gtortone/KeyPortari/firmware/src/PS2Keymaps.cpp

/*
  PS2Keymaps.cpp - PS2Keymaps library
  Copyright (c) 2025 Free Software Foundation.  All right reserved.
  Written by Wolfgang Stubig <w.stubig@firmaplus.de> 2025

  extracted from PS2Keyboard library written by Christian Weichel <info@32leaves.net>
  for more information you can read the original wiki in arduino.cc
  at http://www.arduino.cc/playground/Main/PS2Keyboard
  or http://www.pjrc.com/teensy/td_libs_PS2Keyboard.html
*/

// http://www.quadibloc.com/comp/scan.htm
// http://www.computer-engineering.org/ps2keyboard/scancodes2.html

// These arrays provide a simple key map, to turn scan codes into ISO8859
// output.  For US, DE and FR keyboards.
//

#include "PS2Keymaps.h"

const PROGMEM PS2Keymap_t PS2Keymap_US = {
  // without shift
	{0, PS2_F9, 0, PS2_F5, PS2_F3, PS2_F1, PS2_F2, PS2_F12,
	0, PS2_F10, PS2_F8, PS2_F6, PS2_F4, PS2_TAB, '`', 0,
	0, 0 /*Lalt*/, 0 /*Lshift*/, 0, 0 /*Lctrl*/, 'q', '1', 0,
	0, 0, 'z', 's', 'a', 'w', '2', 0,
	0, 'c', 'x', 'd', 'e', '4', '3', 0,
	0, ' ', 'v', 'f', 't', 'r', '5', 0,
	0, 'n', 'b', 'h', 'g', 'y', '6', 0,
	0, 0, 'm', 'j', 'u', '7', '8', 0,
	0, ',', 'k', 'i', 'o', '0', '9', 0,
	0, '.', '/', 'l', ';', 'p', '-', 0,
	0, 0, '\'', 0, '[', '=', 0, 0,
	0 /*CapsLock*/, 0 /*Rshift*/, PS2_ENTER /*Enter*/, ']', 0, '\\', 0, 0,
	0, 0, 0, 0, 0, 0, PS2_BACKSPACE, 0,
	0, '1', 0, '4', '7', 0, 0, 0,
	'0', '.', '2', '5', '6', '8', PS2_ESC, 0 /*NumLock*/,
	PS2_F11, '+', '3', '-', '*', '9', PS2_SCROLL, 0,
	0, 0, 0, PS2_F7 },
  // with shift
	{0, PS2_F9, 0, PS2_F5, PS2_F3, PS2_F1, PS2_F2, PS2_F12,
	0, PS2_F10, PS2_F8, PS2_F6, PS2_F4, PS2_TAB, '~', 0,
	0, 0 /*Lalt*/, 0 /*Lshift*/, 0, 0 /*Lctrl*/, 'Q', '!', 0,
	0, 0, 'Z', 'S', 'A', 'W', '@', 0,
	0, 'C', 'X', 'D', 'E', '$', '#', 0,
	0, ' ', 'V', 'F', 'T', 'R', '%', 0,
	0, 'N', 'B', 'H', 'G', 'Y', '^', 0,
	0, 0, 'M', 'J', 'U', '&', '*', 0,
	0, '<', 'K', 'I', 'O', ')', '(', 0,
	0, '>', '?', 'L', ':', 'P', '_', 0,
	0, 0, '"', 0, '{', '+', 0, 0,
	0 /*CapsLock*/, 0 /*Rshift*/, PS2_ENTER /*Enter*/, '}', 0, '|', 0, 0,
	0, 0, 0, 0, 0, 0, PS2_BACKSPACE, 0,
	0, '1', 0, '4', '7', 0, 0, 0,
	'0', '.', '2', '5', '6', '8', PS2_ESC, 0 /*NumLock*/,
	PS2_F11, '+', '3', '-', '*', '9', PS2_SCROLL, 0,
	0, 0, 0, PS2_F7 },
	0
};


const PROGMEM PS2Keymap_t PS2Keymap_German = {
  // without shift
	{0, PS2_F9, 0, PS2_F5, PS2_F3, PS2_F1, PS2_F2, PS2_F12,
	0, PS2_F10, PS2_F8, PS2_F6, PS2_F4, PS2_TAB, '^', 0,
	0, 0 /*Lalt*/, 0 /*Lshift*/, 0, 0 /*Lctrl*/, 'q', '1', 0,
	0, 0, 'y', 's', 'a', 'w', '2', 0,
	0, 'c', 'x', 'd', 'e', '4', '3', 0,
	0, ' ', 'v', 'f', 't', 'r', '5', 0,
	0, 'n', 'b', 'h', 'g', 'z', '6', 0,
	0, 0, 'm', 'j', 'u', '7', '8', 0,
	0, ',', 'k', 'i', 'o', '0', '9', 0,
	0, '.', '-', 'l', PS2_o_DIAERESIS, 'p', PS2_SHARP_S, 0,
	0, 0, PS2_a_DIAERESIS, 0, PS2_u_DIAERESIS, '\'', 0, 0,
	0 /*CapsLock*/, 0 /*Rshift*/, PS2_ENTER /*Enter*/, '+', 0, '#', 0, 0,
	0, '<', 0, 0, 0, 0, PS2_BACKSPACE, 0,
	0, '1', 0, '4', '7', 0, 0, 0,
	'0', '.', '2', '5', '6', '8', PS2_ESC, 0 /*NumLock*/,
	PS2_F11, '+', '3', '-', '*', '9', PS2_SCROLL, 0,
	0, 0, 0, PS2_F7 },
  // with shift
	{0, PS2_F9, 0, PS2_F5, PS2_F3, PS2_F1, PS2_F2, PS2_F12,
	0, PS2_F10, PS2_F8, PS2_F6, PS2_F4, PS2_TAB, PS2_DEGREE_SIGN, 0,
	0, 0 /*Lalt*/, 0 /*Lshift*/, 0, 0 /*Lctrl*/, 'Q', '!', 0,
	0, 0, 'Y', 'S', 'A', 'W', '"', 0,
	0, 'C', 'X', 'D', 'E', '$', PS2_SECTION_SIGN, 0,
	0, ' ', 'V', 'F', 'T', 'R', '%', 0,
	0, 'N', 'B', 'H', 'G', 'Z', '&', 0,
	0, 0, 'M', 'J', 'U', '/', '(', 0,
	0, ';', 'K', 'I', 'O', '=', ')', 0,
	0, ':', '_', 'L', PS2_O_DIAERESIS, 'P', '?', 0,
	0, 0, PS2_A_DIAERESIS, 0, PS2_U_DIAERESIS, '`', 0, 0,
	0 /*CapsLock*/, 0 /*Rshift*/, PS2_ENTER /*Enter*/, '*', 0, '\'', 0, 0,
	0, '>', 0, 0, 0, 0, PS2_BACKSPACE, 0,
	0, '1', 0, '4', '7', 0, 0, 0,
	'0', '.', '2', '5', '6', '8', PS2_ESC, 0 /*NumLock*/,
	PS2_F11, '+', '3', '-', '*', '9', PS2_SCROLL, 0,
	0, 0, 0, PS2_F7 },
	1,
  // with altgr
	{0, PS2_F9, 0, PS2_F5, PS2_F3, PS2_F1, PS2_F2, PS2_F12,
	0, PS2_F10, PS2_F8, PS2_F6, PS2_F4, PS2_TAB, 0, 0,
	0, 0 /*Lalt*/, 0 /*Lshift*/, 0, 0 /*Lctrl*/, '@', 0, 0,
	0, 0, 0, 0, 0, 0, PS2_SUPERSCRIPT_TWO, 0,
	0, 0, 0, 0, PS2_CURRENCY_SIGN, 0, PS2_SUPERSCRIPT_THREE, 0,
	0, 0, 0, 0, 0, 0, 0, 0,
	0, 0, 0, 0, 0, 0, 0, 0,
	0, 0, PS2_MICRO_SIGN, 0, 0, '{', '[', 0,
	0, 0, 0, 0, 0, '}', ']', 0,
	0, 0, 0, 0, 0, 0, '\\', 0,
	0, 0, 0, 0, 0, 0, 0, 0,
	0 /*CapsLock*/, 0 /*Rshift*/, PS2_ENTER /*Enter*/, '~', 0, '#', 0, 0,
	0, '|', 0, 0, 0, 0, PS2_BACKSPACE, 0,
	0, '1', 0, '4', '7', 0, 0, 0,
	'0', '.', '2', '5', '6', '8', PS2_ESC, 0 /*NumLock*/,
	PS2_F11, '+', '3', '-', '*', '9', PS2_SCROLL, 0,
	0, 0, 0, PS2_F7 }
};


const PROGMEM PS2Keymap_t PS2Keymap_French = {
  // without shift
	{0, PS2_F9, 0, PS2_F5, PS2_F3, PS2_F1, PS2_F2, PS2_F12,
	0, PS2_F10, PS2_F8, PS2_F6, PS2_F4, PS2_TAB, PS2_SUPERSCRIPT_TWO, 0,
	0, 0 /*Lalt*/, 0 /*Lshift*/, 0, 0 /*Lctrl*/, 'a', '&', 0,
	0, 0, 'w', 's', 'q', 'z', PS2_e_ACUTE, 0,
	0, 'c', 'x', 'd', 'e', '\'', '"', 0,
	0, ' ', 'v', 'f', 't', 'r', '(', 0,
	0, 'n', 'b', 'h', 'g', 'y', '-', 0,
	0, 0, ',', 'j', 'u', PS2_e_GRAVE, '_', 0,
	0, ';', 'k', 'i', 'o', PS2_a_GRAVE, PS2_c_CEDILLA, 0,
	0, ':', '!', 'l', 'm', 'p', ')', 0,
	0, 0, PS2_u_GRAVE, 0, '^', '=', 0, 0,
	0 /*CapsLock*/, 0 /*Rshift*/, PS2_ENTER /*Enter*/, '$', 0, '*', 0, 0,
	0, '<', 0, 0, 0, 0, PS2_BACKSPACE, 0,
	0, '1', 0, '4', '7', 0, 0, 0,
	'0', '.', '2', '5', '6', '8', PS2_ESC, 0 /*NumLock*/,
	PS2_F11, '+', '3', '-', '*', '9', PS2_SCROLL, 0,
	0, 0, 0, PS2_F7 },
  // with shift
	{0, PS2_F9, 0, PS2_F5, PS2_F3, PS2_F1, PS2_F2, PS2_F12,
	0, PS2_F10, PS2_F8, PS2_F6, PS2_F4, PS2_TAB, 0, 0,
	0, 0 /*Lalt*/, 0 /*Lshift*/, 0, 0 /*Lctrl*/, 'A', '1', 0,
	0, 0, 'W', 'S', 'Q', 'Z', '2', 0,
	0, 'C', 'X', 'D', 'E', '4', '3', 0,
	0, ' ', 'V', 'F', 'T', 'R', '5', 0,
	0, 'N', 'B', 'H', 'G', 'Y', '6', 0,
	0, 0, '?', 'J', 'U', '7', '8', 0,
	0, '.', 'K', 'I', 'O', '0', '9', 0,
	0, '/', PS2_SECTION_SIGN, 'L', 'M', 'P', PS2_DEGREE_SIGN, 0,
	0, 0, '%', 0, PS2_DIAERESIS, '+', 0, 0,
	0 /*CapsLock*/, 0 /*Rshift*/, PS2_ENTER /*Enter*/, PS2_POUND_SIGN, 0, PS2_MICRO_SIGN, 0, 0,
	0, '>', 0, 0, 0, 0, PS2_BACKSPACE, 0,
	0, '1', 0, '4', '7', 0, 0, 0,
	'0', '.', '2', '5', '6', '8', PS2_ESC, 0 /*NumLock*/,
	PS2_F11, '+', '3', '-', '*', '9', PS2_SCROLL, 0,
	0, 0, 0, PS2_F7 },
	1,
  // with altgr
	{0, PS2_F9, 0, PS2_F5, PS2_F3, PS2_F1, PS2_F2, PS2_F12,
	0, PS2_F10, PS2_F8, PS2_F6, PS2_F4, PS2_TAB, 0, 0,
	0, 0 /*Lalt*/, 0 /*Lshift*/, 0, 0 /*Lctrl*/, '@', 0, 0,
	0, 0, 0, 0, 0, 0, '~', 0,
	0, 0, 0, 0, 0 /*PS2_EURO_SIGN*/, '{', '#', 0,
	0, 0, 0, 0, 0, 0, '[', 0,
	0, 0, 0, 0, 0, 0, '|', 0,
	0, 0, 0, 0, 0, '`', '\\', 0,
	0, 0, 0, 0, 0, '@', '^', 0,
	0, 0, 0, 0, 0, 0, ']', 0,
	0, 0, 0, 0, 0, 0, '}', 0,
	0 /*CapsLock*/, 0 /*Rshift*/, PS2_ENTER /*Enter*/, '¤', 0, '#', 0, 0,
	0, '|', 0, 0, 0, 0, PS2_BACKSPACE, 0,
	0, '1', 0, '4', '7', 0, 0, 0,
	'0', '.', '2', '5', '6', '8', PS2_ESC, 0 /*NumLock*/,
	PS2_F11, '+', '3', '-', '*', '9', PS2_SCROLL, 0,
	0, 0, 0, PS2_F7 }
};
