gtortone/KeyPortari/src/protocols/parallel_both_BasicProgramming.h

#pragma once

#include <Arduino.h>
#include "../../global.h"
#include "../charsets/BasicProgramming.h"

void protocol_parallel_both_BasicProgramming_setup();
void protocol_parallel_both_BasicProgramming_keyUp();
void protocol_parallel_both_BasicProgramming_keyDown(char value);
