gtortone/KeyPortari/src/protocols/parallel_both_24char.h

#pragma once

#include <Arduino.h>
#include "../../global.h"
#include "../charsets/24char.h"

void protocol_parallel_both_24char_setup();
void protocol_parallel_both_24char_keyUp();
void protocol_parallel_both_24char_keyDown(char value);
